danny-hines/muse-cam/device/tests/test_webapp.py

from __future__ import annotations

import asyncio
import threading
import time
from concurrent.futures import Future
from pathlib import Path

import httpx
import pytest
from aiohttp.test_utils import TestClient, TestServer
from PIL import Image

from musecam.app import FALLBACK_PRESETS, RETIRED_PRESETS
from musecam.config import DeviceConfig, load_profile
from musecam.models import Generation, Preset
from musecam.webapp import CameraWebController, create_web_app


def wait_until(predicate, timeout: float = 6):
    deadline = time.monotonic() + timeout
    while time.monotonic() < deadline:
        result = predicate()
        if result:
            return result
        time.sleep(0.02)
    raise AssertionError("Timed out waiting for camera state")


def make_controller(
    tmp_path: Path, profile_id: str = "pi3bplus-imx415-dsi43"
) -> CameraWebController:
    profiles = Path(__file__).parents[1] / "profiles"
    profile = load_profile(profile_id, profiles)
    config = DeviceConfig(
        server_url="http://127.0.0.1:3000",
        device_token="do-not-expose",
        profile_id=profile.id,
        data_dir=tmp_path,
        profiles_dir=profiles,
    )
    return CameraWebController(config, profile, simulate=True, offline=True)


def test_focus_actions_are_serialized_and_survive_capture(tmp_path):
    controller = make_controller(tmp_path, "pi3bplus-imx519-dsi43")
    controller.start()
    try:
        wait_until(lambda: controller.state()["status"] == "live")
        assert controller.state()["focus"]["supported"]
        controller.dispatch("focus", {"x": 0.25, "y": 0.6})
        wait_until(lambda: controller.state()["focus"]["status"] == "scanning")
        # Even with no MJPEG consumer, a pending focus request must finish.
        wait_until(lambda: controller.state()["focus"]["status"] == "focused")
        revision = controller.state()["revision"]
        controller._refresh_focus()
        assert controller.state()["revision"] == revision
        controller.dispatch("capture")
        wait_until(lambda: controller.state()["galleryCount"] == 1)
        assert controller.state()["focus"]["point"] == {"x": 0.25, "y": 0.6}
        controller.dispatch("focus_auto")
        wait_until(lambda: controller.state()["focus"]["point"] is None)
        assert controller.state()["focus"]["mode"] == "auto"
    finally:
        controller.close()


def test_http_focus_validation_and_unavailable_camera(tmp_path):
    controller = make_controller(tmp_path, "pi3bplus-imx519-dsi43")

    async def exercise():
        async with TestClient(TestServer(create_web_app(controller))) as client:
            controller._start_camera()
            headers = {"X-MuseCam-Request": "1"}
            for values in [{}, {"x": 0.5}, {"x": -1, "y": 1}, {"x": 1.1, "y": 0},
                           {"x": True, "y": 0.5}, {"x": "0.5", "y": 0.5},
                           {"x": None, "y": 0}, {"x": 0, "y": 0, "extra": 1}, []]:
                response = await client.post("/api/actions/focus", json=values, headers=headers)
                assert response.status == 400
            for values in [{"x": 0, "y": 0}, {"x": 1, "y": 1}]:
                response = await client.post("/api/actions/focus", json=values, headers=headers)
                assert response.status == 202
                controller._poll_actions()
            response = await client.post("/api/actions/focus_auto", json={}, headers=headers)
            assert response.status == 202
            controller._poll_actions()
            assert controller.state()["focus"]["point"] is None
            controller._camera_available = False
            response = await client.post(
                "/api/actions/focus", json={"x": 0.5, "y": 0.5}, headers=headers
            )
            assert response.status == 400

    try:
        asyncio.run(exercise())
    finally:
        controller.close()


def test_fixed_focus_profile_does_not_offer_focus_actions(tmp_path):
    controller = make_controller(tmp_path)
    controller._start_camera()
    try:
        assert not controller.state()["focus"]["supported"]
        for x in (float("nan"), float("inf"), 10**1000):
            with pytest.raises(ValueError, match="inside the preview"):
                controller.dispatch("focus", {"x": x, "y": 0.5})
        with pytest.raises(ValueError, match="unavailable"):
            controller.dispatch("focus", {"x": 0.5, "y": 0.5})
    finally:
        controller.close()


@pytest.mark.parametrize(
    ("preset_id", "replacement"),
    [("elven-dawn", "age-of-legends")]
    + [
        (f"disc-2-{variant}", "memory-card")
        for variant in ("smooth", "wide", "smooth-wide", "1996", "reference")
    ],
)
def test_retired_styles_leave_cached_picker_but_keep_gallery_and_retry(
    tmp_path: Path, preset_id: str, replacement: str
) -> None:
    controller = make_controller(tmp_path)
    try:
        controller._store.save_presets([*FALLBACK_PRESETS, *RETIRED_PRESETS.values()])
        controller._store.set_setting("presetId", preset_id)
        controller._load_presets()
        state = controller.state()
        assert not {p["id"] for p in state["presets"]} & RETIRED_PRESETS.keys()
        assert state["preset"]["id"] == replacement

        source = tmp_path / "captures" / "retired.jpg"
        Image.new("RGB", (100, 80), "orange").save(source)
        controller._store.enqueue("retired", preset_id, source)
        controller._store.mark_failed("retired", "Generation failed")
        assert controller.gallery()["items"][0]["presetName"] == RETIRED_PRESETS[preset_id].name
        with pytest.raises(ValueError, match="available style"):
            controller.dispatch("select", {"presetId": preset_id})
        with pytest.raises(ValueError, match="available style"):
            controller._remix({"captureId": "retired", "presetId": preset_id}, retry=False)

        controller._remix({"captureId": "retired"}, retry=True)
        pending = controller._store.pending()
        assert len(pending) == 1
        assert pending[0].preset_id == preset_id
        assert pending[0].source_path != source
        assert pending[0].source_path.read_bytes() == source.read_bytes()
        assert controller._store.get("retired").status == "failed"
    finally:
        controller.close()


@pytest.mark.parametrize("failure", ["capture", "preview"])
def test_camera_error_recovers_and_allows_another_photo(tmp_path, monkeypatch, failure):
    controller = make_controller(tmp_path)
    monkeypatch.setattr("musecam.webapp.CAMERA_RETRY_DELAY", 0.3)
    original = getattr(controller._camera, failure)
    fail_next = threading.Event()

    def interrupt_once(*args):
        if fail_next.is_set():
            fail_next.clear()
            if failure == "capture":
                raise OSError(12, "Cannot allocate memory")
            raise TimeoutError("No preview frame")
        return original(*args)

    monkeypatch.setattr(controller._camera, failure, interrupt_once)
    controller._preview_consumers = 1
    controller.start()
    try:
        wait_until(lambda: controller._preview_jpeg is not None)
        fail_next.set()
        if failure == "capture":
            controller.dispatch("capture")
        wait_until(lambda: controller.state()["status"] == "error")
        assert not controller._camera_available
        assert controller._preview_jpeg is None
        assert controller.state()["message"] != "Hold steady"
        assert controller.state()["galleryCount"] == 0
        assert not list((tmp_path / "captures").iterdir())
        controller.dispatch("next")
        wait_until(lambda: controller.state()["presetIndex"] == 1)
        wait_until(lambda: controller.state()["status"] == "live")
        wait_until(lambda: controller._preview_jpeg is not None)
        assert controller.state()["message"] == ""
        controller.dispatch("capture")
        wait_until(lambda: controller._store.counts().get("complete") == 1)
    finally:
        controller.close()


def test_camera_start_retries_are_bounded_and_manual_restart_works(tmp_path, monkeypatch):
    controller = make_controller(tmp_path)
    monkeypatch.setattr("musecam.webapp.CAMERA_RETRY_DELAY", 0.01)
    original_start = controller._camera.start

    def fail_start():
        raise OSError(12, "Cannot allocate memory")

    monkeypatch.setattr(controller._camera, "start", fail_start)
    controller.start()
    try:
        wait_until(lambda: controller._camera_start_attempts == 3)
        wait_until(lambda: controller._camera_restart_at is None)
        assert controller.state()["status"] == "error"
        assert controller._thread.is_alive()
        # The action loop remains available while the sensor is down.
        controller.dispatch("next")
        wait_until(lambda: controller.state()["presetIndex"] == 1)
        monkeypatch.setattr(controller._camera, "start", original_start)
        controller.dispatch("restart_camera")
        wait_until(lambda: controller.state()["status"] == "live")
        controller.dispatch("capture")
        wait_until(lambda: controller._store.counts().get("complete") == 1)
    finally:
        controller.close()


def test_capture_remains_available_during_generation(tmp_path: Path, monkeypatch) -> None:
    controller = make_controller(tmp_path)
    release = threading.Event()
    entered = threading.Event()
    process = controller._process_job

    def delayed(job):
        entered.set()
        assert release.wait(5)
        return process(job)

    monkeypatch.setattr(controller, "_process_job", delayed)
    controller.start()
    try:
        wait_until(lambda: controller.state()["status"] == "live")
        controller.dispatch("capture")
        assert entered.wait(2)
        first = controller.state()["processingId"]
        next_style = controller.state()["presets"][1]["id"]
        controller.dispatch("select", {"presetId": next_style})
        controller.dispatch("capture")
        # Enqueue publishes the gallery entry just before capture returns to live.
        # Wait for that completed transition while generation is still blocked.
        wait_until(lambda: (
            controller.state()["galleryCount"] == 2
            and controller.state()["status"] == "live"
        ))
        state = controller.state()
        assert state["status"] == "live"
        assert state["processingId"] == first
        assert state["queued"] == 1
        assert controller.gallery()["items"][0]["presetId"] == next_style
        release.set()
        wait_until(lambda: controller._store.counts().get("complete") == 2)
        # The worker commits first; the camera loop then publishes its completion notice.
        wait_until(
            lambda: (
                len([n for n in controller.state()["notifications"] if n["kind"] == "success"]) == 2
            )
        )
        assert controller.state()["status"] == "live"
        assert len([n for n in controller.state()["notifications"] if n["kind"] == "success"]) == 2
    finally:
        release.set()
        controller.close()


def test_gallery_retry_and_restyle_preserve_originals(tmp_path: Path) -> None:
    controller = make_controller(tmp_path)
    source = tmp_path / "captures" / "old.jpg"
    Image.new("RGB", (100, 80), "orange").save(source)
    style = FALLBACK_PRESETS[0].id
    controller._store.enqueue("old", style, source)
    controller._store.mark_failed("old", "Generation failed")
    controller.start()
    try:
        controller.dispatch("retry", {"captureId": "old"})
        wait_until(lambda: controller._store.counts().get("complete") == 1)
        retried = controller.gallery()["items"][0]
        assert retried["id"] != "old"
        assert controller._store.get("old").status == "failed"
        assert controller.media_path(retried["id"], "source").read_bytes() == source.read_bytes()
        assert controller.media_path(retried["id"], "source") != source
        controller.dispatch(
            "remix", {"captureId": retried["id"], "presetId": controller._presets[2].id}
        )
        wait_until(lambda: controller._store.counts().get("complete") == 2)
        newest = controller.gallery()["items"][0]
        assert newest["id"] != retried["id"]
        assert newest["presetId"] == controller._presets[2].id
        assert controller._store.get(retried["id"]).preset_id == style
        assert controller.state()["galleryCount"] == 3
    finally:
        controller.close()


def test_failed_network_job_backs_off_and_allows_new_capture(tmp_path: Path) -> None:
    controller = make_controller(tmp_path)
    controller.start()

    class OfflineClient:
        def generate(self, *args):
            raise httpx.ConnectError("No network")

        def close(self):
            pass

    controller._client = OfflineClient()
    try:
        controller.dispatch("capture")
        wait_until(lambda: bool(controller._retry_after))
        first = next(iter(controller._retry_after))
        assert controller._store.get(first).attempts == 1
        assert controller._store.get(first).status == "queued"
        controller.dispatch("capture")
        wait_until(lambda: len(controller._retry_after) == 2)
        assert controller._store.get(first).attempts == 1
        assert controller.state()["status"] == "live"
        assert controller.state()["networkOnline"] is False
    finally:
        controller.close()


def test_settings_and_history_survive_restart(tmp_path: Path) -> None:
    controller = make_controller(tmp_path)
    controller.save_settings({"volume": 0, "processingSound": False})
    source = tmp_path / "captures" / "persist.jpg"
    Image.new("RGB", (80, 60), "blue").save(source)
    controller._store.enqueue("persist", controller._presets[0].id, source)
    controller._store.mark_uploading("persist")
    session = controller.state()["sessionId"]
    controller.close()
    reopened = make_controller(tmp_path)
    try:
        assert reopened.state()["sessionId"] != session
        assert reopened.state()["volume"] == 0
        assert reopened.state()["processingSound"] is False
        assert reopened.gallery()["items"][0]["status"] == "queued"
        assert reopened.settings()["battery"]["percentage"] is None
        assert reopened.settings()["battery"]["supported"] is False
    finally:
        reopened.close()


def test_delete_removes_one_photo_and_preserves_restyled_original(tmp_path: Path) -> None:
    controller = make_controller(tmp_path)
    source = tmp_path / "captures" / "old.jpg"
    result = tmp_path / "results" / "old.jpg"
    Image.new("RGB", (100, 80), "orange").save(source)
    Image.new("RGB", (100, 80), "blue").save(result)
    style = controller._presets[0].id
    controller._store.enqueue("old", style, source)
    controller._store.mark_complete("old", "generation-old", result, "https://example.com/p/shared")
    controller._remix({"captureId": "old", "presetId": style}, retry=False)
    sibling = controller._store.pending()[0]
    source_bytes = source.read_bytes()
    controller._last_capture_id = controller._last_result_id = "old"
    controller._notify("success", "Ready", "", "old")
    revision = controller.state()["galleryRevision"]
    try:
        controller.delete_photo("old")
        assert not source.exists() and not result.exists()
        assert controller._store.get("old") is None
        assert sibling.source_path.read_bytes() == source_bytes
        assert controller._store.get(sibling.capture_id) is not None
        assert controller.state()["galleryCount"] == 1
        assert controller.state()["galleryRevision"] > revision
        assert controller.state()["lastCaptureId"] is None
        assert controller._last_result_id is None
        assert not any(n["captureId"] == "old" for n in controller.state()["notifications"])
        assert controller.state()["notifications"][-1]["kind"] == "deleted"
        with pytest.raises(ValueError, match="unavailable"):
            controller.media_path("old", "source")
    finally:
        controller.close()
    reopened = make_controller(tmp_path)
    try:
        assert reopened._store.get("old") is None
        assert reopened.state()["galleryCount"] == 1
    finally:
        reopened.close()


@pytest.mark.parametrize("status", ["queued", "failed"])
def test_delete_waiting_or_failed_photo_cleans_partial_download(
    tmp_path: Path, status: str
) -> None:
    controller = make_controller(tmp_path)
    source = tmp_path / "captures" / "old.jpg"
    source.write_bytes(b"original")
    partial = tmp_path / "results" / "old.download"
    partial.write_bytes(b"partial download")
    controller._store.enqueue("old", controller._presets[0].id, source)
    if status == "failed":
        controller._store.mark_failed("old", "Could not finish")
    controller._retry_after["old"] = time.monotonic() + 60
    try:
        controller.delete_photo("old")
        assert not source.exists() and not partial.exists()
        assert "old" not in controller._retry_after
        controller._start_pending()
        assert controller._future is None
        assert controller.state()["galleryCount"] == 0
    finally:
        controller.close()


@pytest.mark.parametrize("busy", ["uploading", "processing", "sharing", "maintenance"])
def test_delete_refuses_busy_photo_without_removing_files(tmp_path: Path, busy: str) -> None:
    controller = make_controller(tmp_path)
    source = tmp_path / "captures" / "busy.jpg"
    source.write_bytes(b"keep me")
    controller._store.enqueue("busy", controller._presets[0].id, source)
    controller._store.mark_failed("busy", "Previous failure")
    if busy == "uploading":
        controller._store.mark_uploading("busy")
    elif busy == "processing":
        controller._processing_id = "busy"  # Worker finished; publication is still pending.
    elif busy == "sharing":
        controller._sharing_id = "busy"
    else:
        controller._maintenance = True
    try:
        with pytest.raises(ValueError):
            controller.delete_photo("busy")
        assert source.read_bytes() == b"keep me"
        assert controller._store.get("busy") is not None
    finally:
        controller.close()


def test_delete_validates_all_paths_and_preserves_shared_legacy_files(tmp_path: Path) -> None:
    controller = make_controller(tmp_path)
    source = tmp_path / "captures" / "shared.jpg"
    source.write_bytes(b"shared original")
    unrelated = tmp_path / "unrelated.txt"
    unrelated.write_bytes(b"not a photo")
    style = controller._presets[0].id
    controller._store.enqueue("one", style, source)
    controller._store.mark_complete("one", "gen-one", unrelated)
    controller._store.enqueue("two", style, source)
    try:
        with pytest.raises(ValueError, match="outside"):
            controller.delete_photo("one")
        assert source.exists() and unrelated.exists()
        result = tmp_path / "results" / "one.jpg"
        result.symlink_to(unrelated)
        controller._store.mark_complete("one", "gen-one", result)
        with pytest.raises(ValueError, match="outside"):
            controller.delete_photo("one")
        assert source.exists() and unrelated.exists()
        result.unlink()
        controller.delete_photo("one")  # Missing result is also tolerated.
        assert source.exists() and unrelated.exists()
        assert controller._store.get("one") is None
        assert controller._store.get("two") is not None
        controller.delete_photo("two")
        assert not source.exists()
        with pytest.raises(ValueError, match="not found"):
            controller.delete_photo("two")
    finally:
        controller.close()


def test_update_is_blocked_with_saved_pending_photos(tmp_path: Path) -> None:
    controller = make_controller(tmp_path)
    try:
        controller._store.enqueue("pending", "style", tmp_path / "pending.jpg")
        with pytest.raises(ValueError, match="queued photos"):
            controller.update()
        assert controller.state()["maintenance"] is False
    finally:
        controller.close()


def test_gallery_filter_finds_failures_older_than_first_page(tmp_path: Path) -> None:
    controller = make_controller(tmp_path)
    try:
        controller._store.enqueue("old-failed", "style", tmp_path / "old.jpg")
        controller._store.mark_failed("old-failed", "Try again")
        for index in range(45):
            controller._store.enqueue(f"new-{index}", "style", tmp_path / "new.jpg")
        assert "old-failed" not in [p["id"] for p in controller.gallery()["items"]]
        assert controller.gallery(status="failed")["items"][0]["id"] == "old-failed"
        assert len(controller.gallery(offset=40, status="waiting")["items"]) == 5
    finally:
        controller.close()


def test_old_device_job_cannot_clear_update_maintenance(tmp_path: Path, monkeypatch) -> None:
    controller = make_controller(tmp_path)
    try:
        controller._maintenance = True
        controller._maintenance_job = "current-update"
        monkeypatch.setattr(
            controller._system,
            "request",
            lambda action: {"job": {"id": "old-wifi", "kind": "wifi", "phase": "complete"}},
        )
        controller.settings()
        assert controller.state()["maintenance"] is True
        monkeypatch.setattr(
            controller._system,
            "request",
            lambda action: {"job": {"id": "current-update", "kind": "update", "phase": "failed"}},
        )
        controller.settings()
        assert controller.state()["maintenance"] is False
    finally:
        controller.close()


def test_preview_slows_when_hot_and_recovers_after_cooling(tmp_path: Path, monkeypatch) -> None:
    controller = make_controller(tmp_path)
    try:
        for temperature, expected in [(78, True), (72, True), (67, False)]:
            monkeypatch.setattr(controller._system, "temperature", lambda value=temperature: value)
            controller._last_battery_read = 0
            controller._refresh_battery()
            assert controller.settings()["previewThrottled"] is expected
            assert controller.settings()["temperature"] == temperature
        assert controller._profile.capture_width == 1920
    finally:
        controller.close()


def test_http_gallery_and_local_settings_boundary(tmp_path: Path) -> None:
    controller = make_controller(tmp_path)
    source = tmp_path / "captures" / "private.jpg"
    Image.new("RGB", (160, 120), "red").save(source)
    controller._store.enqueue("private", controller._presets[0].id, source)
    headers = {"X-MuseCam-Request": "1"}

    async def exercise():
        async with TestClient(TestServer(create_web_app(controller))) as client:
            assert (await client.post("/api/settings", json={"volume": 0})).status == 403
            assert (
                await client.post(
                    "/api/settings",
                    json={"volume": 0},
                    headers={**headers, "Origin": "https://evil.example"},
                )
            ).status == 403
            assert (
                await client.get("/api/settings", headers={"Host": "evil.example"})
            ).status == 403
            response = await client.post("/api/settings", json={"volume": 0}, headers=headers)
            assert response.status == 200
            assert (await response.json())["volume"] == 0
            assert (
                await client.post("/api/settings", json={"volume": 999}, headers=headers)
            ).status == 400
            for path, body in [
                ("/api/settings", []),
                ("/api/sound", []),
                ("/api/sound", {"cue": []}),
                ("/api/system/wifi-scan", {"action": "update-apply"}),
            ]:
                assert (await client.post(path, json=body, headers=headers)).status == 400
            response = await client.get("/api/gallery")
            item = (await response.json())["items"][0]
            assert item["id"] == "private"
            assert "do-not-expose" not in await (await client.get("/api/state")).text()
            assert (await client.get(item["sourceUrl"])).status == 200
            assert (await client.get(item["thumbnailUrl"])).content_type == "image/jpeg"
            assert (await client.get("/api/gallery/missing")).status == 404
            assert (await client.get("/api/gallery/private/result")).status == 400
            delete_url = "/api/gallery/private/delete"
            assert (await client.post(delete_url, json={})).status == 403
            assert (
                await client.post(
                    delete_url, json={}, headers={**headers, "Origin": "https://evil.example"}
                )
            ).status == 403
            assert source.exists()
            response = await client.post(delete_url, json={}, headers=headers)
            assert response.status == 200
            assert (await response.json())["deleted"] is True
            assert not source.exists()
            assert (await client.get("/api/gallery/private")).status == 404
            assert (await client.get(item["sourceUrl"])).status == 400
            assert (await client.get("/api/gallery")).status == 200
            assert (await client.post(delete_url, json={}, headers=headers)).status == 400

    try:
        asyncio.run(exercise())
    finally:
        controller.close()


def test_shutdown_ends_open_event_and_preview_streams(tmp_path: Path) -> None:
    controller = make_controller(tmp_path)
    controller.start()

    async def exercise():
        client = TestClient(TestServer(create_web_app(controller)))
        await client.start_server()
        events = await client.get("/api/events")
        preview = await client.get("/preview.mjpg")
        await events.content.readline()
        await preview.content.readline()
        try:
            await asyncio.wait_for(client.server.close(), timeout=3)
            assert controller._stop.is_set()
        finally:
            await client.close()

    try:
        asyncio.run(exercise())
    finally:
        controller.close()


def test_deleted_photo_retraction_retries_after_restart(tmp_path, monkeypatch):
    controller = make_controller(tmp_path)
    source = tmp_path / "captures" / "sync.jpg"
    source.write_bytes(b"local photo")
    controller._store.enqueue("capture-sync", "kid-drawing", source)
    controller._store.mark_complete(
        "capture-sync", "generation-sync", tmp_path / "results" / "sync.jpg",
        "https://camera.example/p/shared",
    )

    class SyncClient:
        def __init__(self, fail=False):
            self.fail = fail
            self.calls = []

        def retract_capture(self, capture_id):
            self.calls.append(capture_id)
            if self.fail:
                raise httpx.ConnectError("offline")

        def close(self):
            pass

    failing = SyncClient(fail=True)
    controller._client = failing
    try:
        controller.delete_photo("capture-sync")
        assert not source.exists()
        assert controller._store.get("capture-sync") is None
        assert controller.state()["pendingRetractions"] == 1
        controller._sync_retractions()
        wait_until(lambda: controller._retraction_future.done())
        controller._sync_retractions()
        assert failing.calls == ["capture-sync"]
        assert controller.state()["pendingRetractions"] == 1
    finally:
        controller.close()

    reopened = make_controller(tmp_path)
    succeeding = SyncClient()
    reopened._client = succeeding
    try:
        monkeypatch.setattr("musecam.store.time.time", lambda: 99999999999)
        reopened._sync_retractions()
        wait_until(lambda: reopened._retraction_future.done())
        reopened._sync_retractions()
        assert succeeding.calls == ["capture-sync"]
        assert reopened.state()["pendingRetractions"] == 0
    finally:
        reopened.close()


def test_deleting_an_interrupted_upload_retracts_without_a_generation_id(tmp_path):
    controller = make_controller(tmp_path)
    controller._offline = False
    source = tmp_path / "captures" / "interrupted.jpg"
    source.write_bytes(b"photo")
    try:
        controller._store.enqueue("capture-interrupted", "kid-drawing", source)
        controller._store.mark_uploading("capture-interrupted")
        controller._store.mark_queued("capture-interrupted", "Upload response was lost")
        controller.delete_photo("capture-interrupted")
        assert controller._store.pending_retraction() == "capture-interrupted"
    finally:
        controller.close()


def test_auto_shared_generation_is_recorded_in_camera_gallery(tmp_path):
    from musecam.models import Generation

    controller = make_controller(tmp_path)
    source = tmp_path / "captures" / "auto.jpg"
    Image.new("RGB", (80, 60), "blue").save(source)
    controller._store.enqueue("capture-auto", "kid-drawing", source)

    class AutoShareClient:
        def generate(self, image, capture_id, preset_id):
            return Generation(
                "generation-auto", capture_id, "complete", preset_id,
                "https://camera.example/image", "https://camera.example/p/auto", None,
            )

        def download_result(self, url, output):
            Image.new("RGB", (80, 60), "red").save(output, "JPEG")

        def close(self):
            pass

    controller._client = AutoShareClient()
    try:
        outcome = controller._process_job(controller._store.get("capture-auto"))
        assert outcome.job.share_url == "https://camera.example/p/auto"
        assert controller.gallery()["items"][0]["shareUrl"] == outcome.job.share_url
    finally:
        controller.close()


def test_random_style_resolves_each_shot_and_retry_keeps_the_choice(tmp_path, monkeypatch):
    controller = make_controller(tmp_path)
    controller._load_presets()
    controller._start_camera()
    styles = iter(FALLBACK_PRESETS[:3])
    choices = []

    def choose(options):
        assert all(p.id != "random" and p.id not in RETIRED_PRESETS for p in options)
        selected = next(styles)
        choices.append(selected.id)
        return selected

    monkeypatch.setattr("musecam.webapp.random.choice", choose)
    try:
        assert controller.state()["presets"][0]["id"] == "random"
        controller._handle_action("select", {"presetId": "random"})
        controller._handle_action("capture", {})
        first = controller._store.get(controller.state()["lastCaptureId"])
        controller._handle_action("capture", {})
        second = controller._store.get(controller.state()["lastCaptureId"])
        assert first.preset_id == FALLBACK_PRESETS[0].id
        assert second.preset_id == FALLBACK_PRESETS[1].id
        assert controller.state()["preset"]["id"] == "random"
        controller._store.mark_failed(first.capture_id, "Try again")
        controller._remix({"captureId": first.capture_id}, retry=True)
        retry = controller.gallery()["items"][0]
        assert retry["presetId"] == first.preset_id
        assert len(choices) == 2
        controller._remix({"captureId": first.capture_id, "presetId": "random"}, retry=False)
        assert controller.gallery()["items"][0]["presetId"] == FALLBACK_PRESETS[2].id
        controller._load_presets()
        assert controller.state()["preset"]["id"] == "random"
    finally:
        controller.close()


def test_a_single_server_style_has_no_random_entry(tmp_path):
    controller = make_controller(tmp_path)
    surprise = Preset(
        id="surprise", version=1, name="Surprise",
        description="A different style for every photo, picked for you.", accent="#d6b8ff",
    )
    controller._store.save_presets([surprise])
    controller._store.set_setting("presetId", "random")
    controller._load_presets()
    controller._start_camera()
    try:
        state = controller.state()
        assert [p["id"] for p in state["presets"]] == ["surprise"]
        assert state["preset"]["id"] == "surprise"
        with pytest.raises(ValueError, match="available style"):
            controller.dispatch("select", {"presetId": "random"})
        controller._handle_action("capture", {})
        shot = controller._store.get(controller.state()["lastCaptureId"])
        assert shot.preset_id == "surprise"
        controller._remix({"captureId": shot.capture_id, "presetId": "surprise"}, retry=False)
        assert controller.gallery()["items"][0]["presetName"] == "Surprise"
    finally:
        controller.close()


def test_surprise_photos_are_labeled_with_the_style_the_server_picked(tmp_path):
    controller = make_controller(tmp_path)
    surprise = Preset(
        id="surprise", version=1, name="Surprise",
        description="A different style for every photo, picked for you.", accent="#d6b8ff",
    )
    controller._store.save_presets([surprise])
    controller._load_presets()

    class SurpriseClient:
        def generate(self, image, capture_id, preset_id):
            assert preset_id == "surprise"
            return Generation(
                "generation-surprise", capture_id, "complete", "muse-mode",
                "https://camera.example/image", None, None, preset_name="Muse Mode",
            )

        def download_result(self, url, output):
            Image.new("RGB", (80, 60), "red").save(output, "JPEG")

        def close(self):
            pass

    source = tmp_path / "captures" / "surprise.jpg"
    Image.new("RGB", (100, 80), "orange").save(source)
    controller._store.enqueue("capture-surprise", "surprise", source)
    controller._client = SurpriseClient()
    try:
        outcome = controller._process_job(controller._store.get("capture-surprise"))
        assert (outcome.job.preset_id, outcome.job.preset_name) == ("muse-mode", "Muse Mode")
        item = controller.gallery()["items"][0]
        assert (item["presetId"], item["presetName"]) == ("muse-mode", "Muse Mode")
        finished = Future()
        finished.set_result(outcome)
        controller._future, controller._processing_id = finished, "capture-surprise"
        controller._poll_future()
        assert controller.state()["notifications"][-1]["message"] == "Muse Mode"
    finally:
        controller.close()


@pytest.mark.parametrize("seconds", [5, 10])
def test_shutter_counts_down_beeps_once_per_second_and_captures_once(
    tmp_path, monkeypatch, seconds
):
    controller = make_controller(tmp_path)
    controller._start_camera()
    clock = [100.0]
    monkeypatch.setattr("musecam.webapp.time.monotonic", lambda: clock[0])
    cues = []
    monkeypatch.setattr(controller._sound, "play", cues.append)
    try:
        controller._handle_action("select", {"presetId": FALLBACK_PRESETS[0].id})
        controller._handle_action("timer", {})
        if seconds == 10:
            controller._handle_action("timer", {})
        assert controller.state()["timerSeconds"] == seconds
        controller.dispatch("capture")  # The same action used by the GPIO shutter.
        controller._poll_actions()
        deadline = controller._countdown_deadline
        assert controller.state()["countdownRemaining"] == seconds
        assert controller.state()["status"] == "countdown"
        controller.dispatch("capture")
        controller._poll_actions()
        assert controller._countdown_deadline == deadline
        # A style change cannot alter the shot already counting down.
        controller._handle_action("select", {"presetId": FALLBACK_PRESETS[1].id})
        for elapsed in range(1, seconds):
            clock[0] = 100.0 + elapsed
            controller._poll_countdown()
            controller._poll_countdown()  # Repeated frames must not beep twice.
            assert controller.state()["countdownRemaining"] == seconds - elapsed
            assert controller.state()["galleryCount"] == 0
        clock[0] = deadline - 0.001
        controller._poll_countdown()
        assert controller.state()["galleryCount"] == 0
        clock[0] = deadline
        controller._poll_countdown()
        controller._poll_countdown()
        assert cues == ["countdown"] * seconds + ["shutter"]
        assert controller.state()["galleryCount"] == 1
        assert controller.state()["countdownRemaining"] == 0
        assert controller.state()["status"] == "live"
        assert controller.gallery()["items"][0]["presetId"] == FALLBACK_PRESETS[0].id
    finally:
        controller.close()


@pytest.mark.parametrize("cancel", ["cancel_capture", "camera_failure", "power", "close"])
def test_countdown_cancellation_never_takes_a_late_photo(tmp_path, monkeypatch, cancel):
    controller = make_controller(tmp_path)
    controller._start_camera()
    clock = [100.0]
    monkeypatch.setattr("musecam.webapp.time.monotonic", lambda: clock[0])
    try:
        controller._handle_action("timer", {})
        controller._handle_action("capture", {})
        with pytest.raises(ValueError, match="queued photos"):
            controller.update()
        if cancel == "camera_failure":
            controller._camera_failed()
        elif cancel == "close":
            controller._stop.set()
        else:
            controller._handle_action(cancel, {})
        clock[0] = 120.0
        controller._poll_countdown()
        assert controller.state()["galleryCount"] == 0
        if cancel != "close":
            assert controller.state()["countdownRemaining"] == 0
    finally:
        controller.close()


def test_timer_cycles_and_off_takes_an_immediate_photo(tmp_path):
    controller = make_controller(tmp_path)
    controller._start_camera()
    try:
        assert controller.state()["timerSeconds"] == 0
        for value in (5, 10, 0):
            controller._handle_action("timer", {})
            assert controller.state()["timerSeconds"] == value
        controller._handle_action("capture", {})
        assert controller.state()["galleryCount"] == 1
        controller._handle_action("timer", {})
    finally:
        controller.close()
    reopened = make_controller(tmp_path)
    try:
        assert reopened.state()["timerSeconds"] == 5
        assert reopened.state()["countdownRemaining"] == 0
    finally:
        reopened.close()


@pytest.mark.parametrize("screen", ["gallery", "photo"])
@pytest.mark.parametrize("seconds", [0, 5, 10])
def test_gallery_shutter_returns_to_camera_before_capturing(tmp_path, monkeypatch, screen, seconds):
    controller = make_controller(tmp_path)
    controller._start_camera()
    controller._store.enqueue("existing", FALLBACK_PRESETS[0].id, tmp_path / "existing.jpg")
    cues = []
    monkeypatch.setattr(controller._sound, "play", cues.append)
    try:
        for _ in range(seconds // 5):
            controller._handle_action("timer", {})
        controller.dispatch("view", {"screen": screen, "photoId": "existing"})
        controller._poll_actions()
        assert controller.state()["view"]["screen"] == screen

        # Exercise the GPIO action path, without relying on a browser key handler.
        controller.dispatch("capture")
        controller._poll_actions()
        assert controller.state()["view"] == {"screen": "camera", "photoId": None}
        assert controller.state()["galleryCount"] == 1
        assert controller.state()["lastCaptureId"] is None
        assert controller.state()["status"] == "live"
        assert controller.state()["countdownRemaining"] == 0
        assert cues == []

        controller.dispatch("capture")
        controller._poll_actions()
        if seconds:
            assert controller.state()["countdownRemaining"] == seconds
            assert controller.state()["status"] == "countdown"
            assert controller.state()["galleryCount"] == 1
            assert cues == ["countdown"]
        else:
            assert controller.state()["galleryCount"] == 2
            assert controller.state()["lastCaptureId"] is not None
            assert cues == ["shutter"]
    finally:
        controller.close()


def test_view_action_validates_screens_and_photos(tmp_path):
    controller = make_controller(tmp_path)
    try:
        for values in ({}, {"screen": "missing"}, {"screen": ["gallery"]}):
            with pytest.raises(ValueError, match="available screen"):
                controller.dispatch("view", values)
        with pytest.raises(ValueError, match="Photo was not found"):
            controller.dispatch("view", {"screen": "photo", "photoId": "missing"})
        assert controller.state()["view"] == {"screen": "camera", "photoId": None}
    finally:
        controller.close()


def test_detail_neighbors_cross_pages_and_respect_gallery_filters(tmp_path):
    controller = make_controller(tmp_path)
    for index in range(45):
        capture_id = f"photo-{index:02d}"
        controller._store.enqueue(capture_id, FALLBACK_PRESETS[0].id, tmp_path / capture_id)
        if index % 2 == 0:
            controller._store.mark_failed(capture_id, "test")

    async def exercise():
        async with TestClient(TestServer(create_web_app(controller))) as client:
            detail = await (await client.get("/api/gallery/photo-05")).json()
            assert detail["previousId"] == "photo-06"
            assert detail["nextId"] == "photo-04"
            oldest = await (await client.get("/api/gallery/photo-00")).json()
            assert oldest["nextId"] is None
            newest = await (await client.get("/api/gallery/photo-44")).json()
            assert newest["previousId"] is None
            filtered = await (await client.get("/api/gallery/photo-06?filter=failed")).json()
            assert filtered["previousId"] == "photo-08"
            assert filtered["nextId"] == "photo-04"
            controller._store.delete("photo-04")
            after_delete = await (await client.get("/api/gallery/photo-06?filter=failed")).json()
            assert after_delete["nextId"] == "photo-02"

    try:
        asyncio.run(exercise())
    finally:
        controller.close()
