danny-hines/muse-cam/device/tests/test_app.py

from __future__ import annotations

from unittest.mock import Mock

import httpx
import pytest
from PIL import Image

from musecam.app import (
    CAMERA_UNAVAILABLE_MESSAGE,
    MuseCamApp,
    api_error_code,
    friendly_generation_error,
)
from musecam.models import Action, ScreenState
from musecam.store import CaptureStore


def test_reads_generation_error_code_from_api_response() -> None:
    request = httpx.Request("POST", "https://camera.example/api/device/generations")
    response = httpx.Response(
        422,
        json={"error": "filtered", "details": {"code": "content_filtered"}},
        request=request,
    )
    error = httpx.HTTPStatusError("filtered", request=request, response=response)

    assert api_error_code(error) == "content_filtered"
    assert friendly_generation_error(api_error_code(error)) == (
        "Try another style or framing. Tap BACK."
    )


@pytest.mark.parametrize("action", (Action.BACK, Action.SHUTTER, Action.SHARE))
def test_error_controls_return_to_live_view(action: Action) -> None:
    app = object.__new__(MuseCamApp)
    app._camera_available = True
    app._state = ScreenState.ERROR
    app._message = "Remix failed"
    app._result = Image.new("RGB", (2, 2))

    app._handle_action(action)

    assert app._state == ScreenState.LIVE
    assert app._message == ""
    assert app._result is None


def test_error_cannot_hide_an_unavailable_camera() -> None:
    app = object.__new__(MuseCamApp)
    app._camera_available = False
    app._state = ScreenState.ERROR
    app._message = CAMERA_UNAVAILABLE_MESSAGE
    app._result = None

    app._handle_action(Action.BACK)

    assert app._state == ScreenState.ERROR
    assert app._message == CAMERA_UNAVAILABLE_MESSAGE


def test_shutter_leaves_native_photo_review_before_capturing() -> None:
    app = object.__new__(MuseCamApp)
    app._camera_available = True
    app._state = ScreenState.RESULT
    app._message = ""
    app._result = Image.new("RGB", (2, 2))
    app._capture = Mock()

    app._handle_action(Action.SHUTTER)
    assert app._state == ScreenState.LIVE
    assert app._result is None
    app._capture.assert_not_called()

    app._handle_action(Action.SHUTTER)
    app._capture.assert_called_once_with()


def test_native_camera_retries_temporary_auto_share_failure(tmp_path):
    app = object.__new__(MuseCamApp)
    app._store = CaptureStore(tmp_path / "captures.sqlite3")
    app._results_dir = tmp_path
    app._store.enqueue("capture-native", "kid-drawing", tmp_path / "source.jpg")

    class BusyClient:
        def generate(self, *args):
            request = httpx.Request("POST", "https://camera.example/api/device/generations")
            response = httpx.Response(503, request=request)
            response.raise_for_status()

    app._client = BusyClient()
    try:
        result = app._process_job(app._store.get("capture-native"))
        assert result.queued is True
        assert result.job.status == "queued"
    finally:
        app._store.close()
